Insper/turtlebot3/Garra/garra-direita.stl

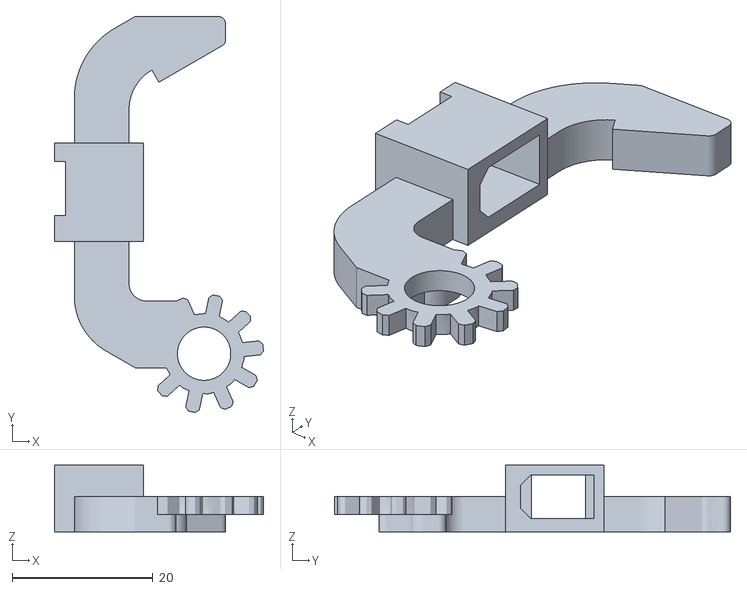
[picture p23: CAD file, 2019-12-20]
Garra/garra-direita.stl
29.8 x 56.4 x 9.50
