Insper/turtlebot3/Suportes_Turtlebot3/Suporte_Camera_RaspBerry/Suporte_servo_camera.dxf

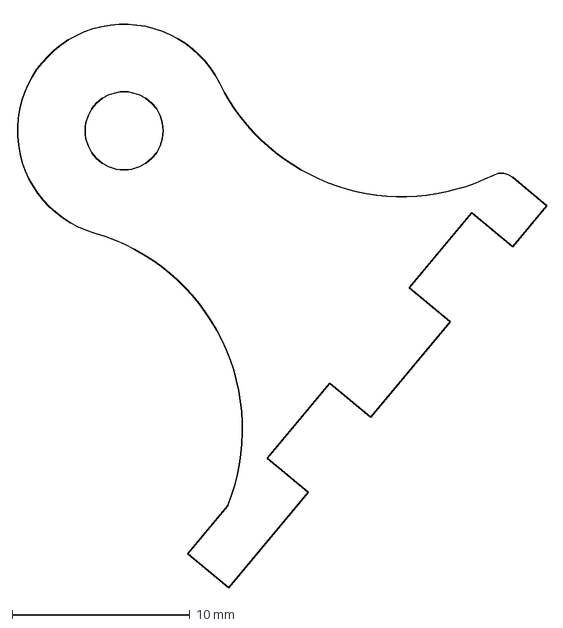
[picture p24: CAD file, 2019-03-27]
Suportes_Turtlebot3/Suporte_Camera_RaspBerry/Suporte_servo_camera.dxf
29.9 x 32.2 mm
