Insper/turtlebot3/Suportes_Turtlebot3/Suporte_Garra/SuporteGarra-P1update.stl

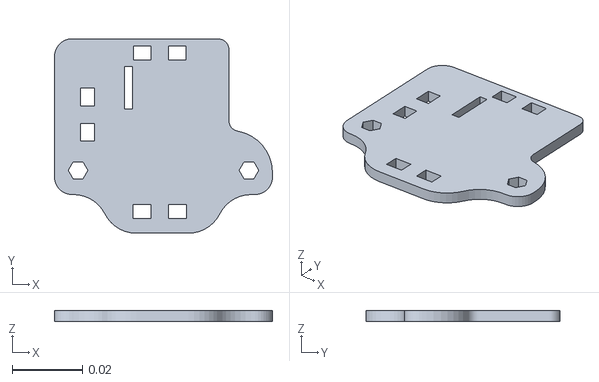
[picture p25: CAD file, 2019-10-09]
Suportes_Turtlebot3/Suporte_Garra/SuporteGarra-P1update.stl
0.062 x 0.0553 x 0.003
