Insper/turtlebot3/Suportes_Turtlebot3/Suporte_OLED _ Botoes/Suporte_Lateral_OLED.dxf

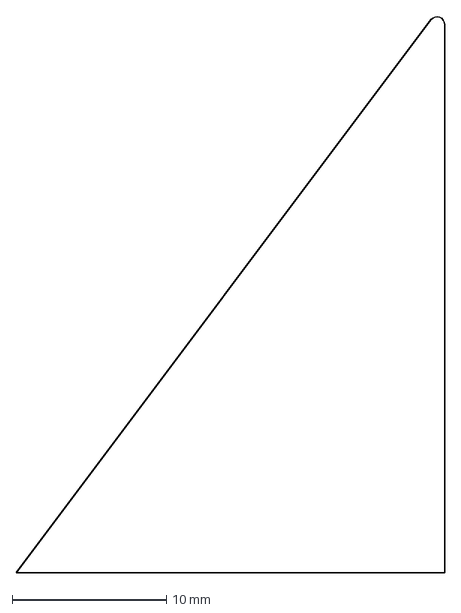
[picture p26: CAD file, 2019-03-27]
Suportes_Turtlebot3/Suporte_OLED _ Botoes/Suporte_Lateral_OLED.dxf
27.8 x 36.1 mm
