Insper/turtlebot3/Suportes_Turtlebot3/Suporte_RealSense/Suporte_RealSense_Lateral.dxf

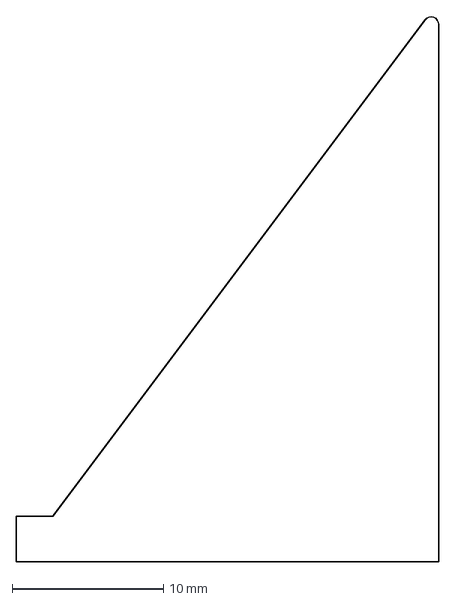
[picture p27: CAD file, 2019-03-27]
Suportes_Turtlebot3/Suporte_RealSense/Suporte_RealSense_Lateral.dxf
27.9 x 36.1 mm
