Insper/turtlebot3/Garra/garrabraco-REBAIXO.stl

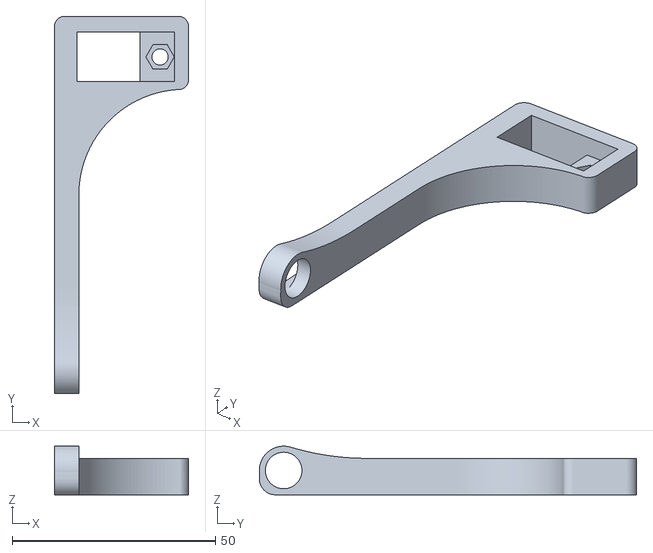
[picture p28: CAD file, 2019-10-09]
Garra/garrabraco-REBAIXO.stl
33.0 x 92.9 x 12.0
