Insper/turtlebot3/Suportes_Turtlebot3/Suporte_Garra/SuporteGarra-P2.stl

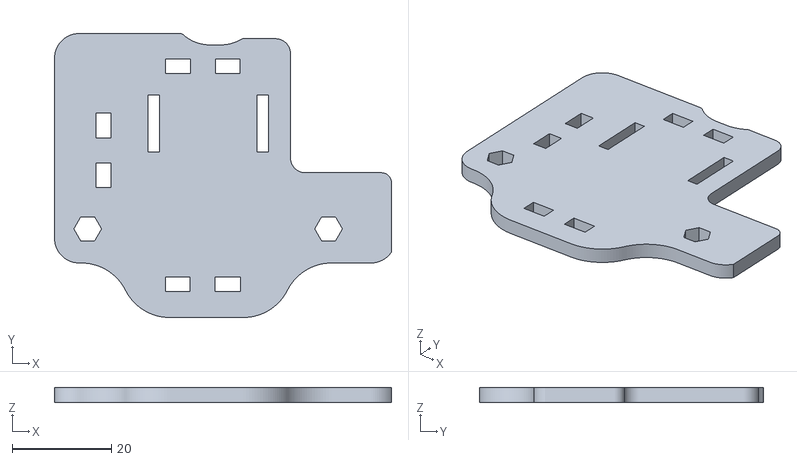
[picture p29: CAD file, 2019-10-09]
Suportes_Turtlebot3/Suporte_Garra/SuporteGarra-P2.stl
68.0 x 57.3 x 3.00
