Insper/turtlebot3/Suportes_Turtlebot3/Suporte_Garra/SuporteGarra-P1.stl

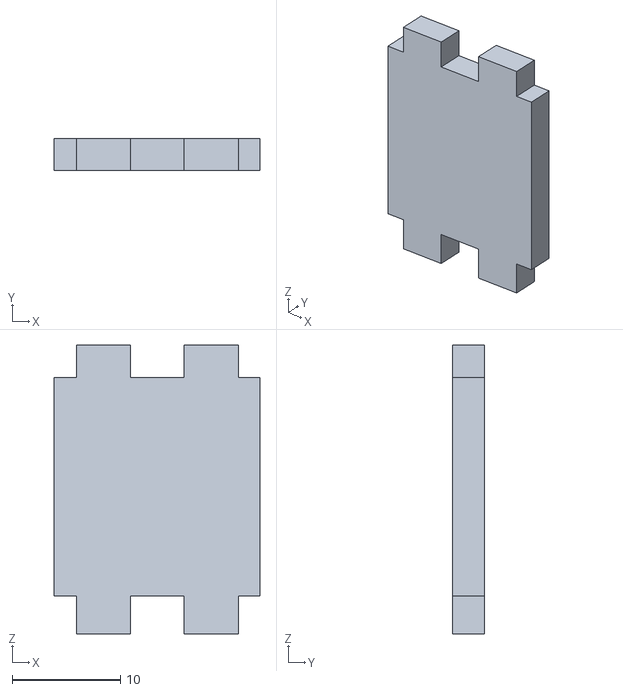
[picture p30: CAD file, 2019-10-09]
Suportes_Turtlebot3/Suporte_Garra/SuporteGarra-P1.stl
19.0 x 3.00 x 26.7
